grinje/AutoSatTracker/AutoSatTracker-ESP32/wmm.h

static double epoc = 2020.0;
const double c0[13][13]={
{	0.0,	-29404.5,	-2500.0,	1363.9,	903.1,	-234.4,	65.9,	80.6,	23.6,	5.0,	-1.9,	3.0,	-2.0,	},
{	4652.9,	-1450.7,	2982.0,	-2381.0,	809.4,	363.1,	65.6,	-76.8,	9.8,	8.2,	-6.2,	-1.4,	-0.1,	},
{	-2991.6,	-734.8,	1676.8,	1236.2,	86.2,	187.8,	73.0,	-8.3,	-17.5,	2.9,	-0.1,	-2.5,	0.5,	},
{	-82.2,	241.8,	-542.9,	525.7,	-309.4,	-140.7,	-121.5,	56.5,	-0.4,	-1.4,	1.7,	2.4,	1.3,	},
{	282.0,	-158.4,	199.8,	-350.1,	47.9,	-151.2,	-36.2,	15.8,	-21.1,	-1.1,	-0.9,	-0.9,	-1.2,	},
{	47.7,	208.4,	-121.3,	32.2,	99.1,	13.7,	13.5,	6.4,	15.3,	-13.3,	0.6,	0.3,	0.7,	},
{	-19.1,	25.0,	52.7,	-64.4,	9.0,	68.1,	-64.7,	-7.2,	13.7,	1.1,	-0.9,	-0.7,	0.3,	},
{	-51.4,	-16.8,	2.3,	23.5,	-2.2,	-27.2,	-1.9,	9.8,	-16.5,	8.9,	1.9,	-0.1,	0.5,	},
{	8.4,	-15.3,	12.8,	-11.8,	14.9,	3.6,	-6.9,	2.8,	-0.3,	-9.3,	1.4,	1.4,	-0.2,	},
{	-23.3,	11.1,	9.8,	-5.1,	-6.2,	7.8,	0.4,	-1.5,	9.7,	-11.9,	-2.4,	-0.6,	-0.5,	},
{	3.4,	-0.2,	3.5,	4.8,	-8.6,	-0.1,	-4.2,	-3.4,	-0.1,	-8.8,	-3.9,	0.2,	0.1,	},
{	-0.0,	2.6,	-0.5,	-0.4,	0.6,	-0.2,	-1.7,	-1.6,	-3.0,	-2.0,	-2.6,	3.1,	-1.1,	},
{	-1.2,	0.5,	1.3,	-1.8,	0.1,	0.7,	-0.1,	0.6,	0.2,	-0.9,	-0.0,	0.5,	-0.3,	},
};
const double cd0[13][13]={
{	0.0,	6.7,	-11.5,	2.8,	-1.1,	-0.3,	-0.6,	-0.1,	-0.1,	-0.1,	0.0,	-0.0,	0.0,	},
{	-25.1,	7.7,	-7.1,	-6.2,	-1.6,	0.6,	-0.4,	-0.3,	0.1,	-0.2,	-0.0,	-0.1,	-0.0,	},
{	-30.2,	-23.9,	-2.2,	3.4,	-6.0,	-0.7,	0.5,	-0.1,	-0.1,	-0.0,	-0.0,	-0.0,	-0.0,	},
{	5.7,	-1.0,	1.1,	-12.2,	5.4,	0.1,	1.4,	0.7,	0.5,	0.4,	0.2,	0.0,	0.0,	},
{	0.2,	6.9,	3.7,	-5.6,	-5.5,	1.2,	-1.4,	0.2,	-0.1,	-0.3,	-0.1,	-0.0,	-0.0,	},
{	0.1,	2.5,	-0.9,	3.0,	0.5,	1.0,	-0.0,	-0.5,	0.4,	-0.0,	-0.2,	-0.1,	-0.0,	},
{	0.1,	-1.8,	-1.4,	0.9,	0.1,	1.0,	0.8,	-0.8,	0.5,	0.3,	-0.0,	0.0,	0.0,	},
{	0.5,	0.6,	-0.7,	-0.2,	-1.2,	0.2,	0.3,	1.0,	0.0,	-0.0,	-0.1,	-0.0,	-0.0,	},
{	-0.3,	0.7,	-0.2,	0.5,	-0.3,	-0.5,	0.4,	0.1,	0.4,	-0.0,	-0.2,	-0.1,	0.0,	},
{	-0.3,	0.2,	-0.4,	0.4,	0.1,	-0.0,	-0.2,	0.5,	0.2,	-0.4,	-0.1,	-0.1,	-0.0,	},
{	-0.0,	0.1,	-0.3,	0.1,	-0.2,	0.1,	-0.0,	-0.1,	0.2,	-0.0,	-0.0,	-0.1,	-0.0,	},
{	-0.0,	0.1,	0.0,	0.2,	-0.0,	0.0,	0.1,	-0.0,	-0.1,	0.0,	-0.0,	-0.1,	-0.0,	},
{	-0.0,	0.0,	-0.1,	0.1,	-0.0,	0.0,	-0.0,	0.1,	-0.0,	-0.0,	0.0,	-0.1,	-0.1,	},
};
